SartoriDynamics/Self-Balancing-Omni-Bike/3D printing/Files/left_body.stl

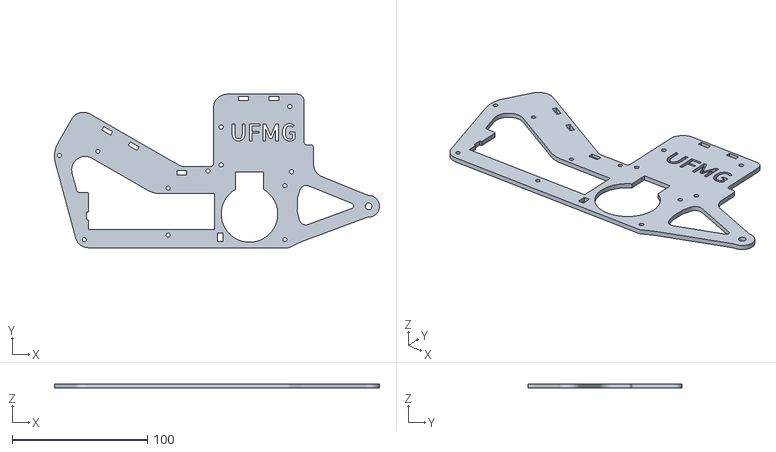
[picture p18: CAD file, 2025-11-03]
3D printing/Files/left_body.stl
240.4 x 113.6 x 3.00
